iSebass/TourisTech/micropython_codes/boot.py

# This file is executed on every boot (including wake-boot from deepsleep)
#import esp
#esp.osdebug(None)
#import webrepl
#webrepl.start()

def getSSID():
    return "Docentes"

def getPASS():
    return "KIZqBsUf8m"

def getToken():
    return "BBFF-BRvJm1Ba7u0t1eUTXGgYFzPKK44Wkt"
